otokarbalcy/Electronic-Filter-Wheel-EFW-52/Images/25-10-01 07-52-46 6390.jpg

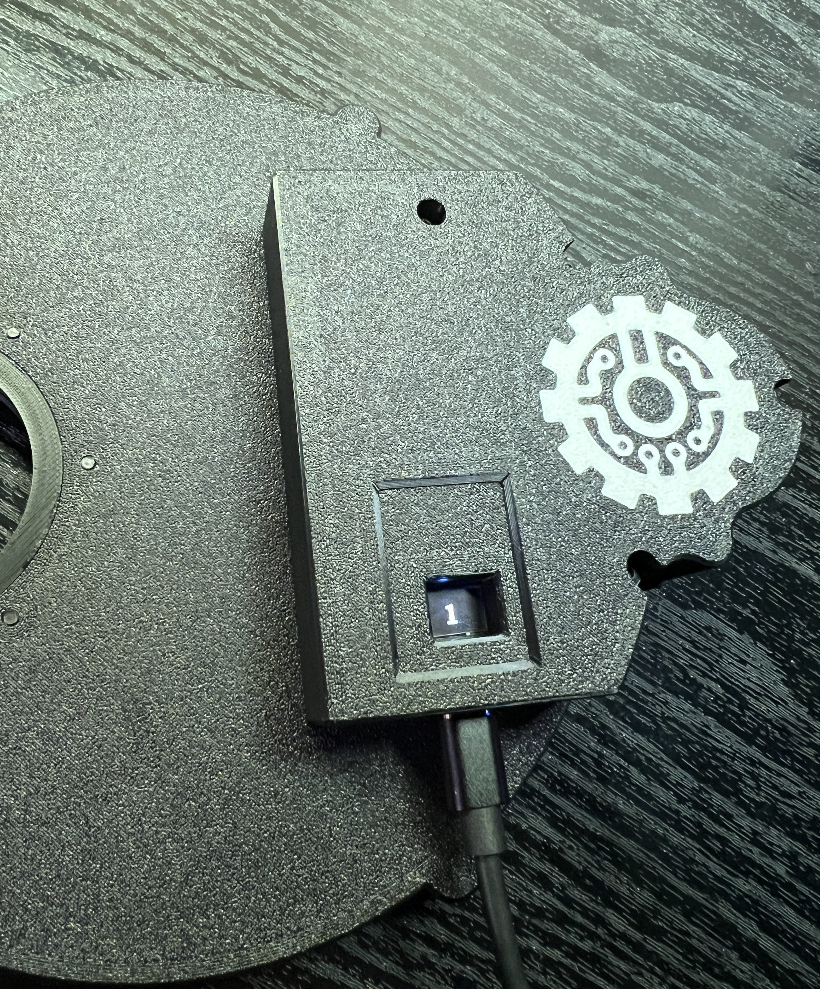
Images/25-10-01 07-52-46 6390.jpg
