otokarbalcy/Electronic-Filter-Wheel-EFW-52/Images/25-10-01 07-52-53 6391.jpg

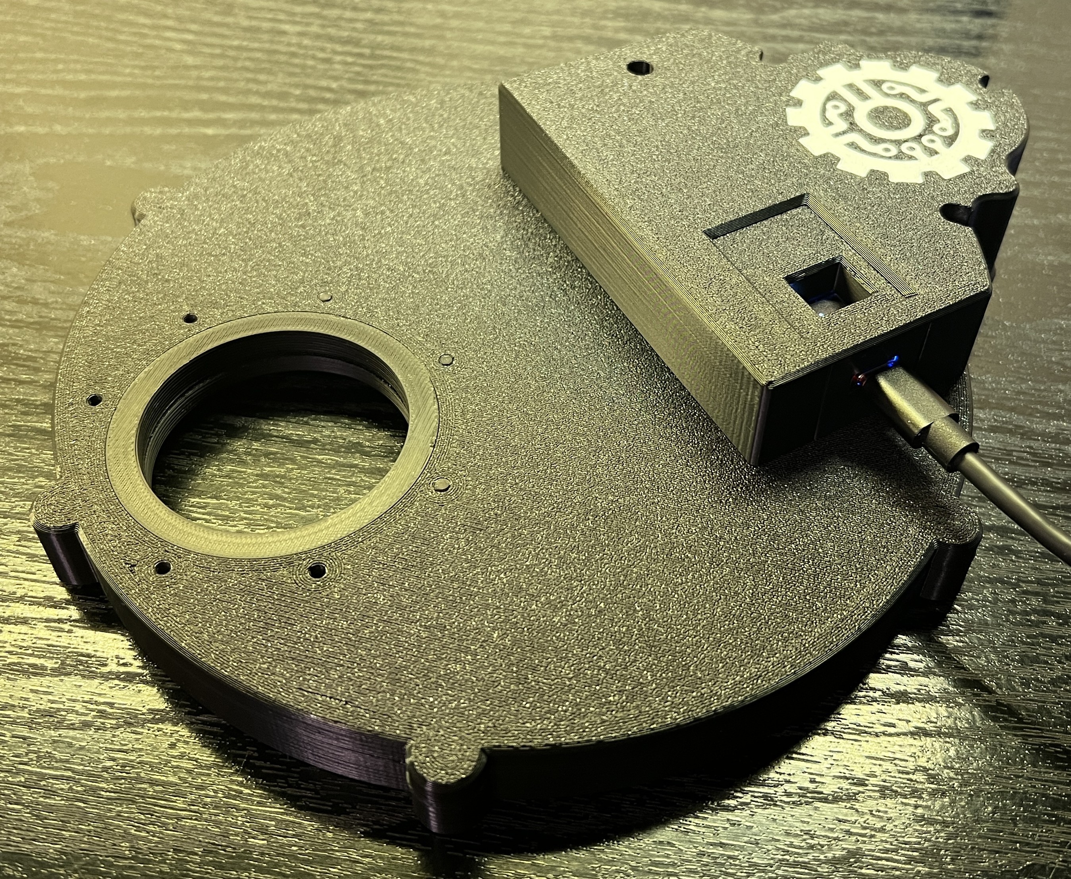
Images/25-10-01 07-52-53 6391.jpg
