otokarbalcy/Electronic-Filter-Wheel-EFW-52/Images/25-10-01 11-04-11 6400.jpg

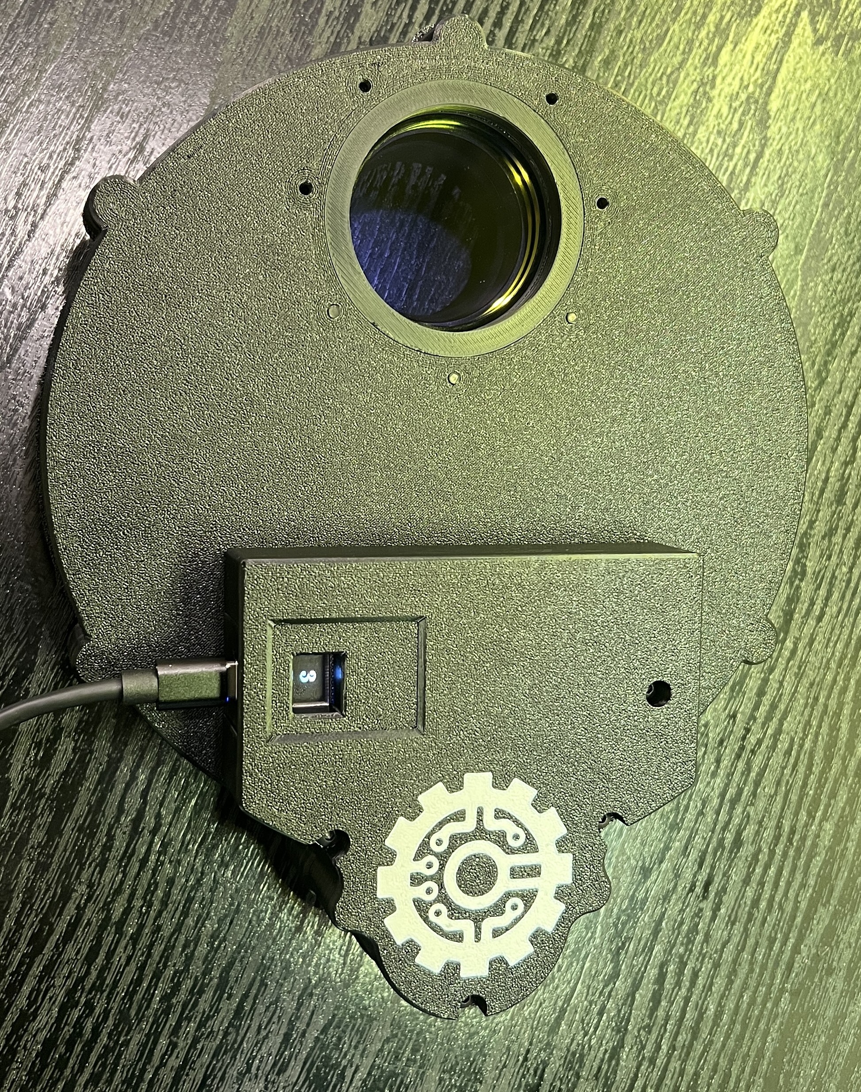
Images/25-10-01 11-04-11 6400.jpg
