otokarbalcy/Electronic-Filter-Wheel-EFW-52/Images/25-10-01 11-04-27 6401.jpg

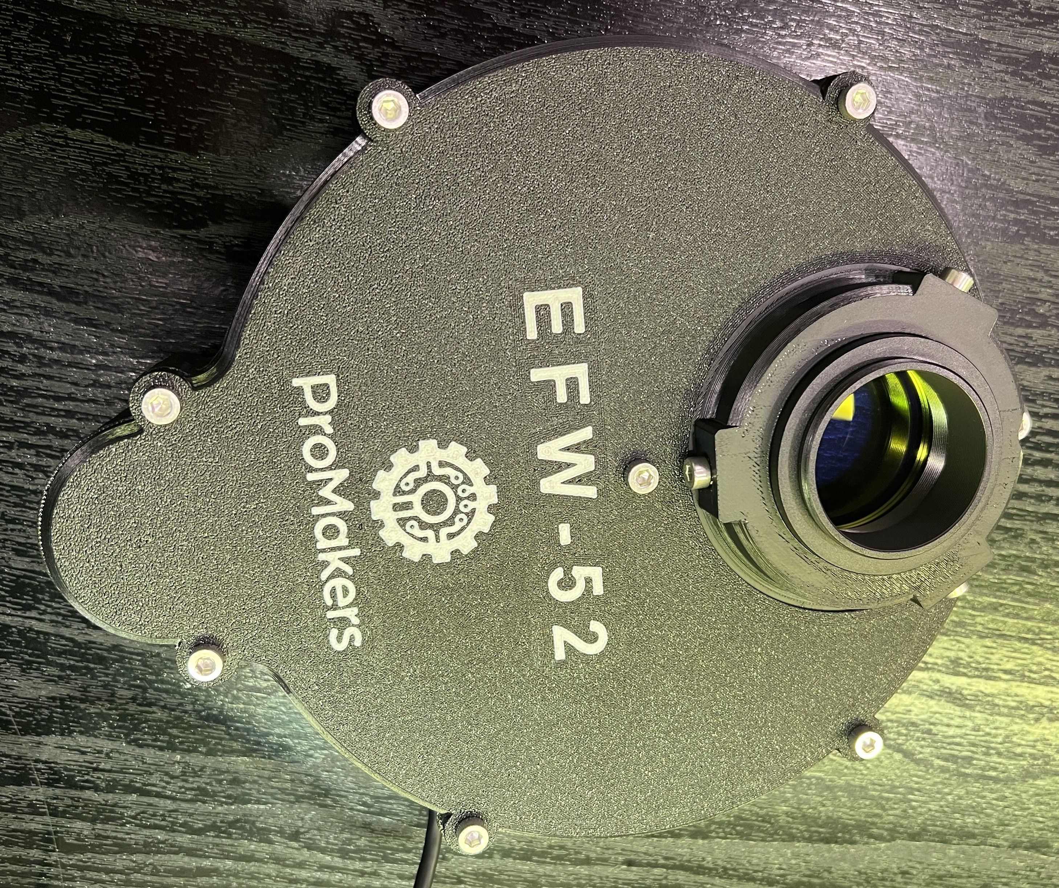
Images/25-10-01 11-04-27 6401.jpg
