otokarbalcy/Electronic-Filter-Wheel-EFW-52/Images/25-10-01 11-05-17 6402.jpg

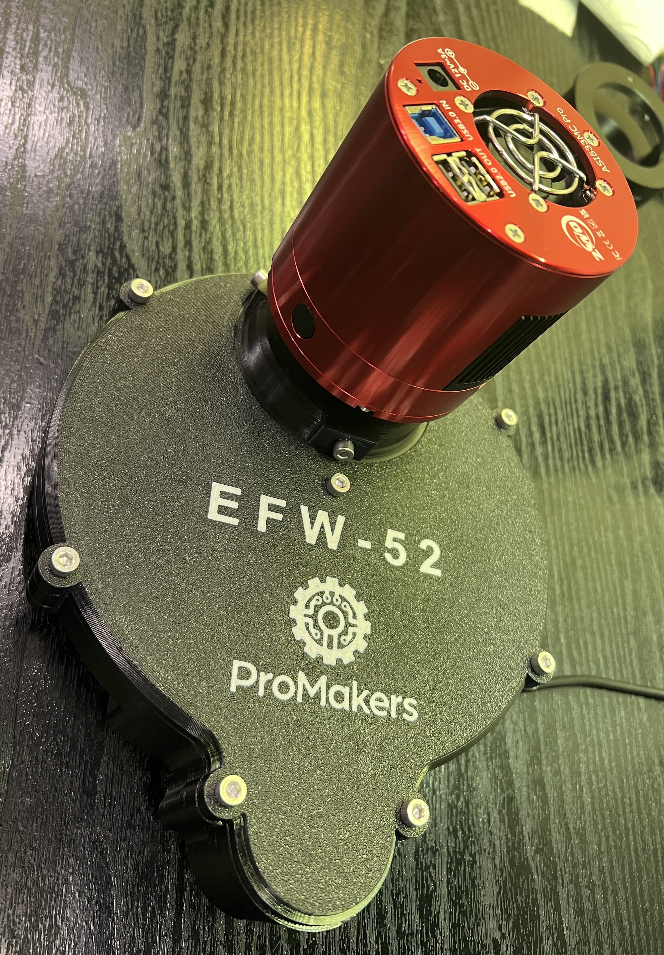
Images/25-10-01 11-05-17 6402.jpg
