otokarbalcy/Electronic-Filter-Wheel-EFW-52/Images/25-10-01 11-08-09 6405.jpg

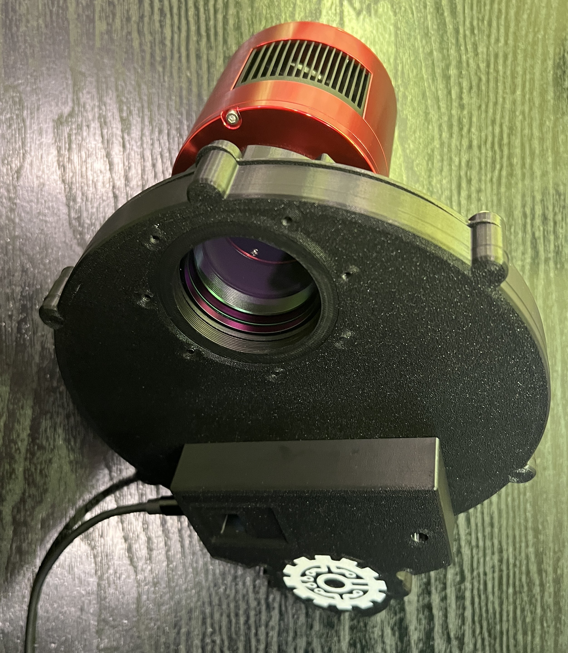
Images/25-10-01 11-08-09 6405.jpg
