otokarbalcy/Electronic-Filter-Wheel-EFW-52/Images/25-10-01 11-08-12 6406.jpg

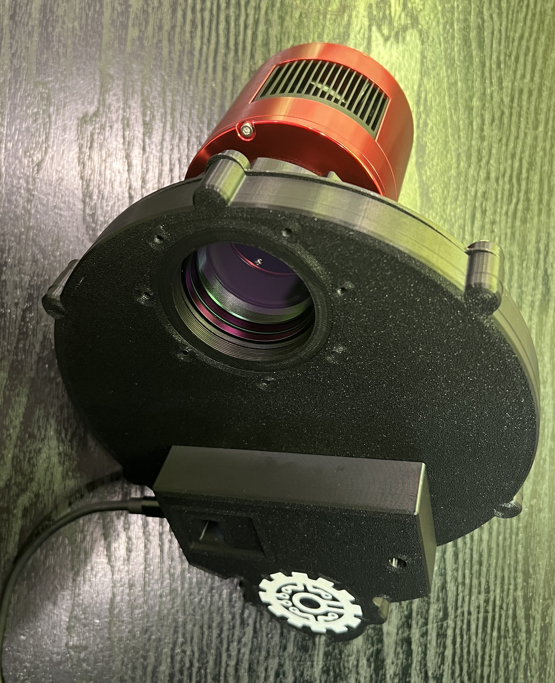
Images/25-10-01 11-08-12 6406.jpg
