otokarbalcy/Electronic-Filter-Wheel-EFW-52/Images/25-10-01 11-44-52 6412.jpg

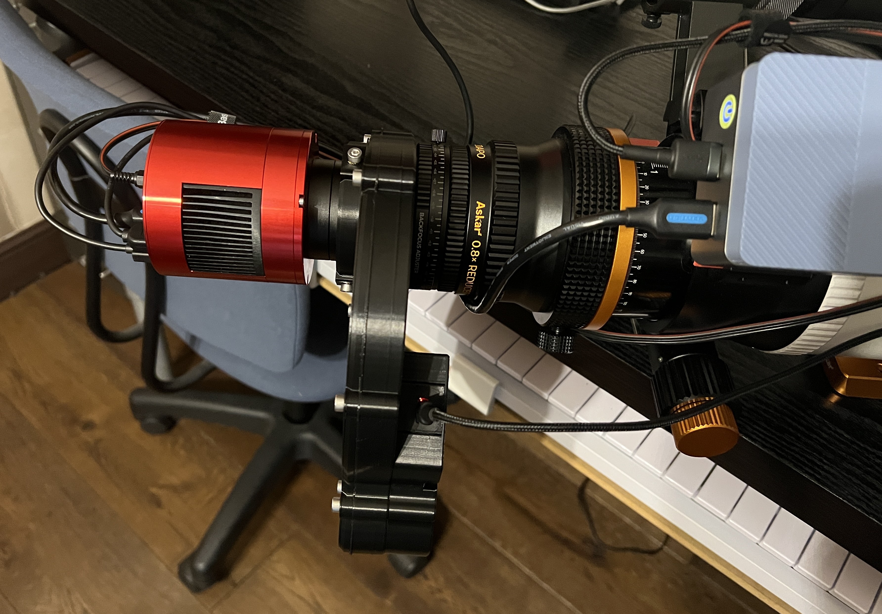
Images/25-10-01 11-44-52 6412.jpg
